androportal/anuduino/doc/images/digitermlm35.png

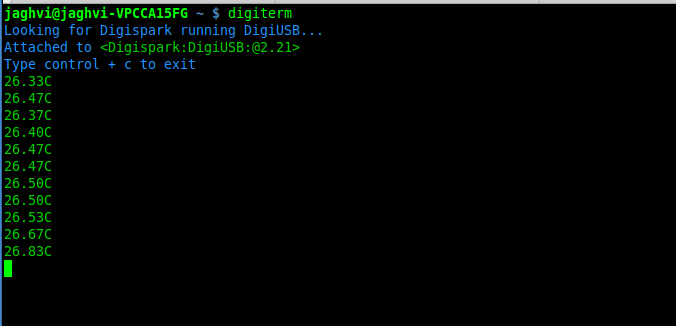
doc/images/digitermlm35.png
