androportal/anuduino/doc/images/errousb.png

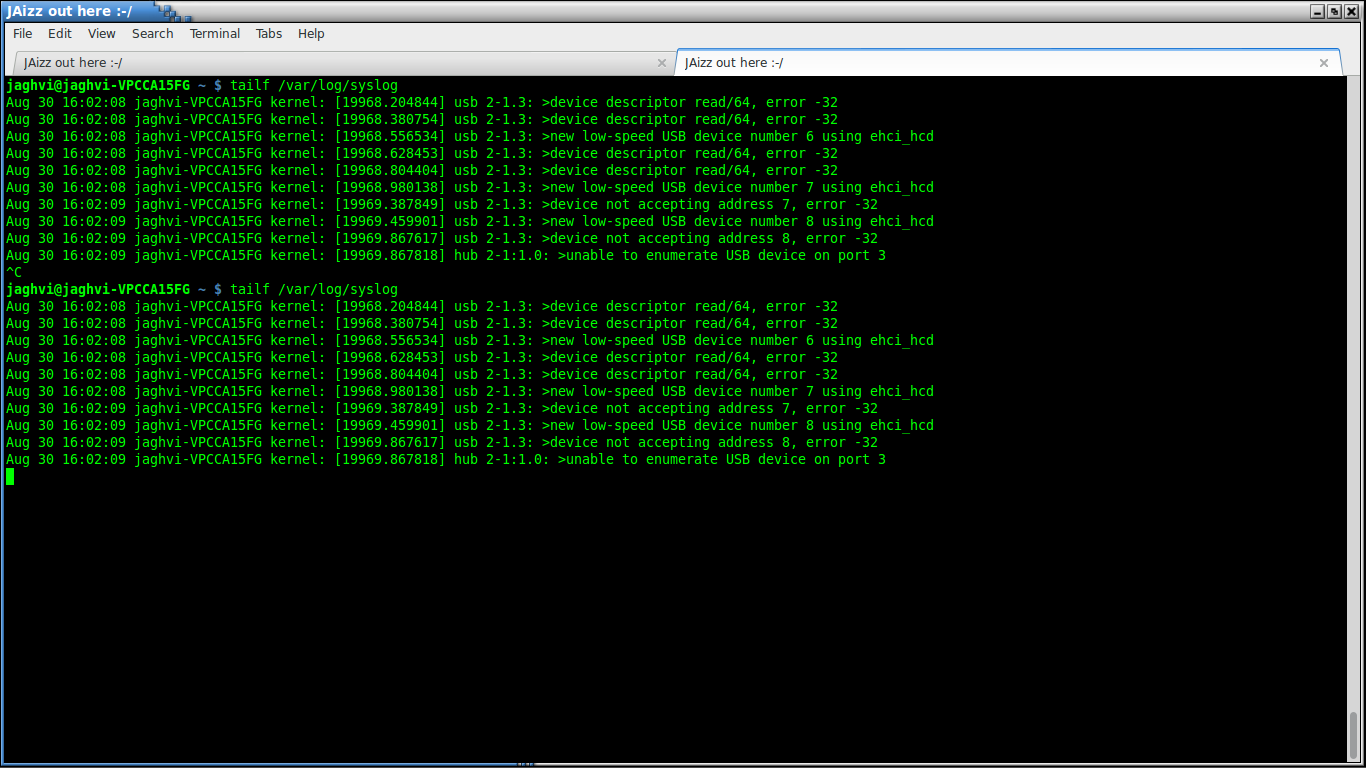
doc/images/errousb.png
